Lescurel/pear_lamp/lamp.scad

include <modules.scad>


lamp();
