Lescurel/pear_lamp/lower.scad

include <modules.scad>

lower_part();
