Lescurel/pear_lamp/middle.scad

include <modules.scad>


middle_part();
