Lescurel/pear_lamp/upper.scad

include <modules.scad>


upper_part();
